danromero1/Mixed-Signal-Guitar-Effects-Pedal/docs/images/mixed_signal_final_3d_shot.png

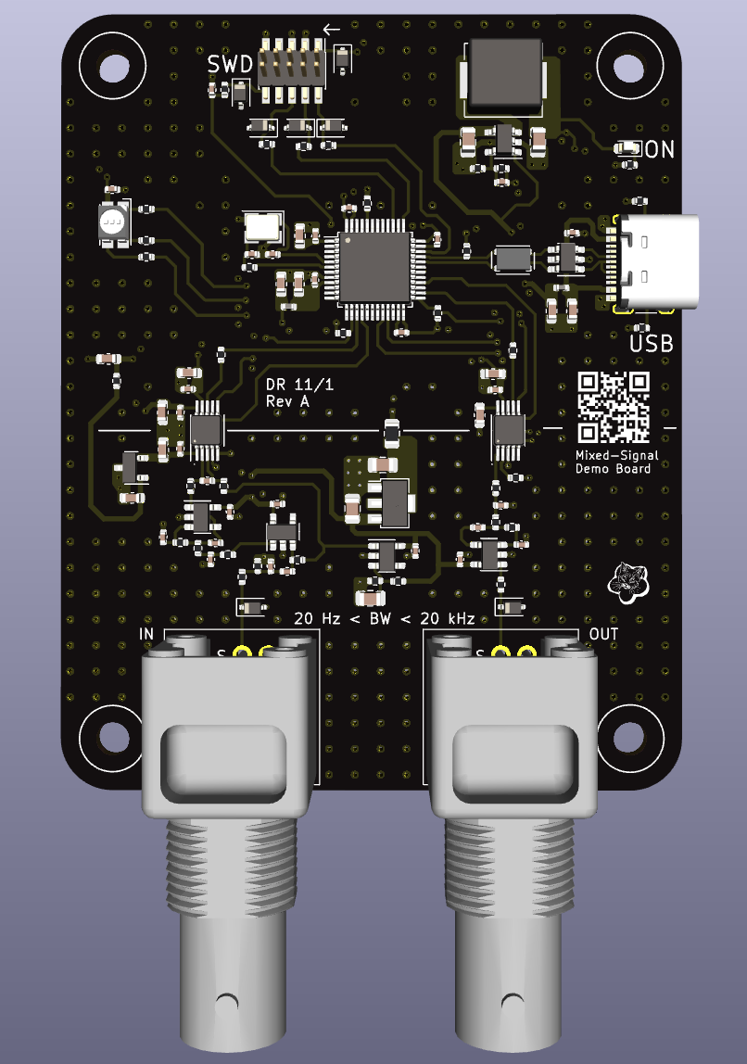
docs/images/mixed_signal_final_3d_shot.png
